thingSoC/TSOC_Teensy3x/TSOC_Teensy3x/eagleUp/eagleUp_TSOC_Teensy3X_board_bottom.jpg

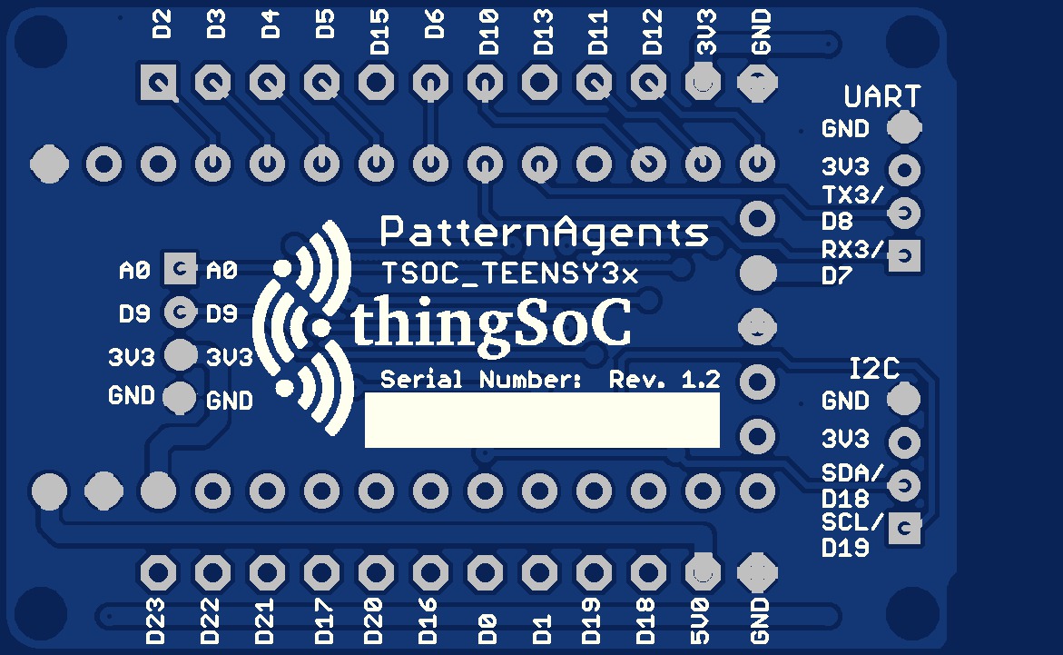
TSOC_Teensy3x/eagleUp/eagleUp_TSOC_Teensy3X_board_bottom.jpg
