thingSoC/TSOC_Teensy3x/TSOC_Teensy3x/eagleUp/eagleUp_TSOC_Teensy3X_board_top.jpg

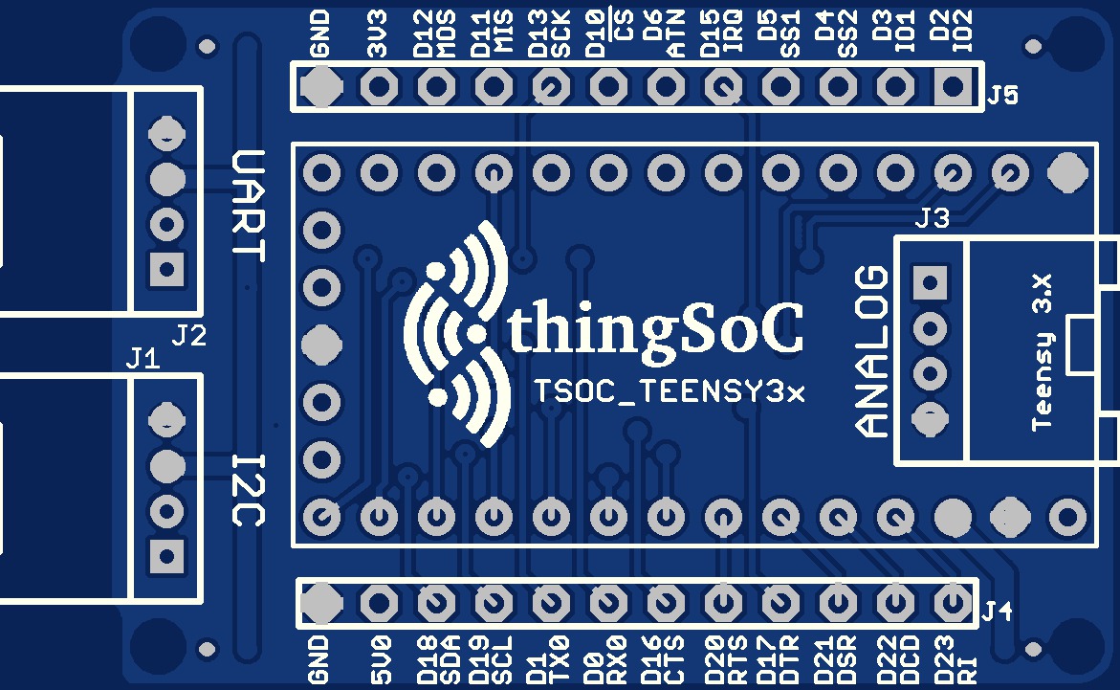
TSOC_Teensy3x/eagleUp/eagleUp_TSOC_Teensy3X_board_top.jpg
