thingSoC/TSOC_Teensy3x/TSOC_Teensy3x/images/product/TSOC_Teensy3x_click.jpg

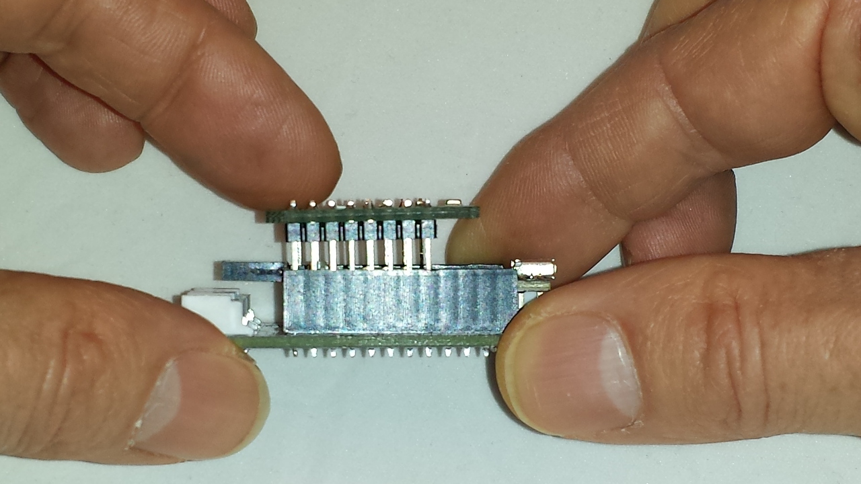
TSOC_Teensy3x/images/product/TSOC_Teensy3x_click.jpg
