thingSoC/TSOC_Teensy3x/TSOC_Teensy3x/images/product/TSOC_Teensy3x_pcb.png

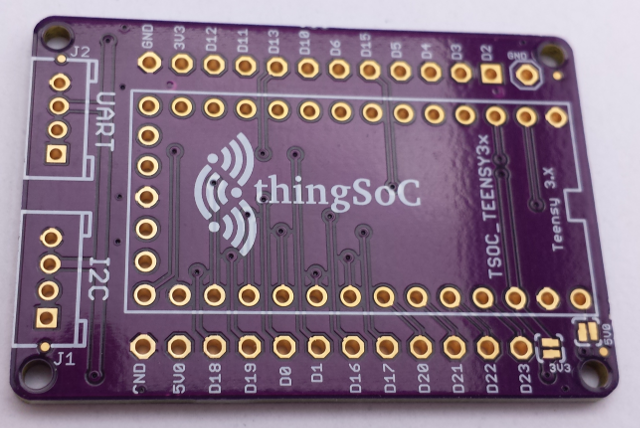
TSOC_Teensy3x/images/product/TSOC_Teensy3x_pcb.png
