thingSoC/TSOC_Teensy3x/TSOC_Teensy3x/images/product/TSOC_Teensy3x_pop_top.png

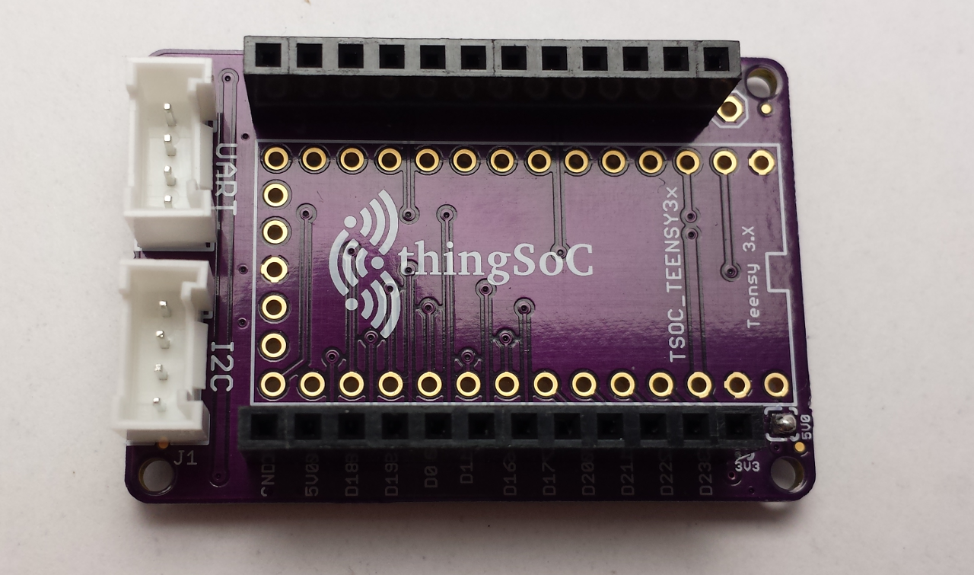
TSOC_Teensy3x/images/product/TSOC_Teensy3x_pop_top.png
