thingSoC/TSOC_Teensy3x/TSOC_Teensy3x/images/product/TSOC_Teensy3x_R1_0.png

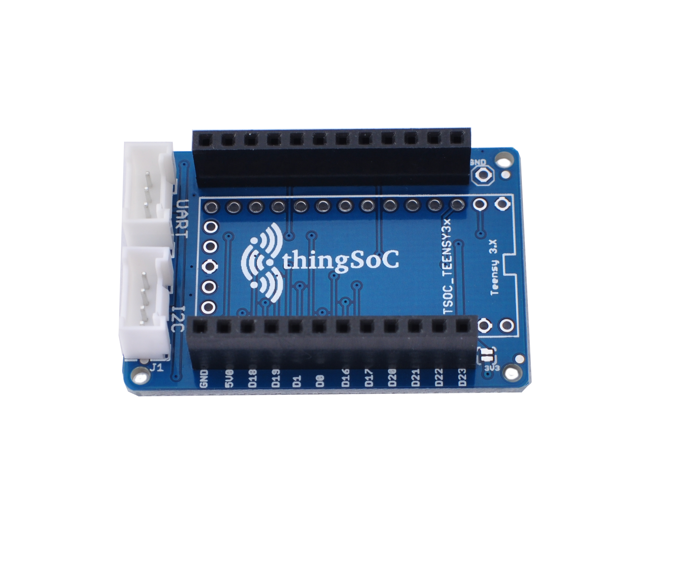
TSOC_Teensy3x/images/product/TSOC_Teensy3x_R1_0.png
