thingSoC/TSOC_Teensy3x/TSOC_Teensy3x/images/product/TSOC_Teensy3x_USB1.jpg

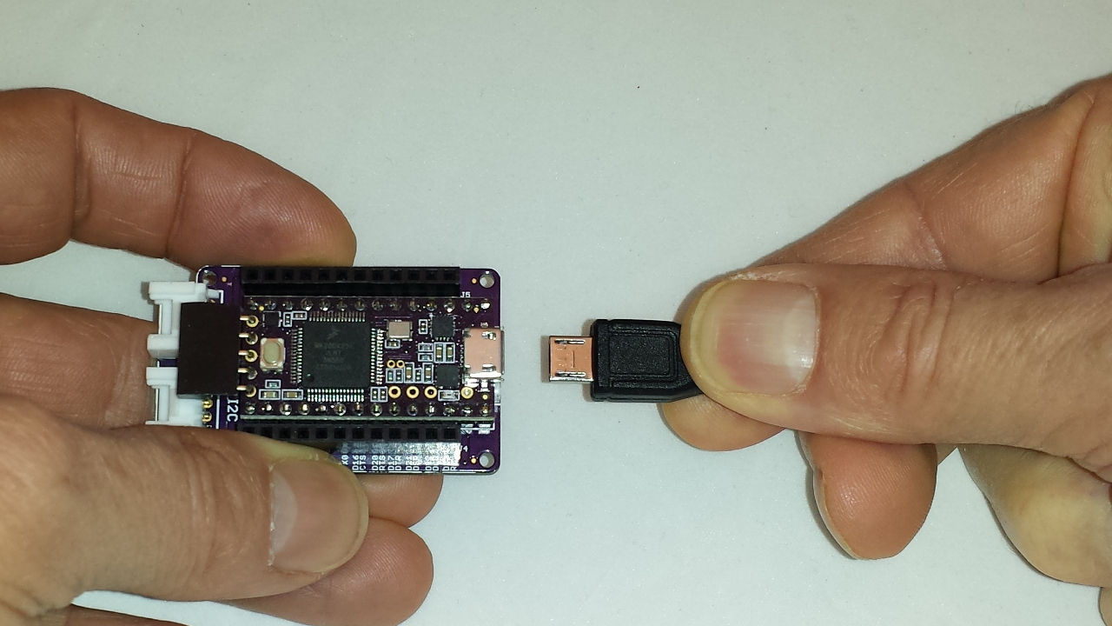
TSOC_Teensy3x/images/product/TSOC_Teensy3x_USB1.jpg
