thingSoC/TSOC_Teensy3x/TSOC_Teensy3x/images/product/TSOC_Teensy3x_with_Click3.png

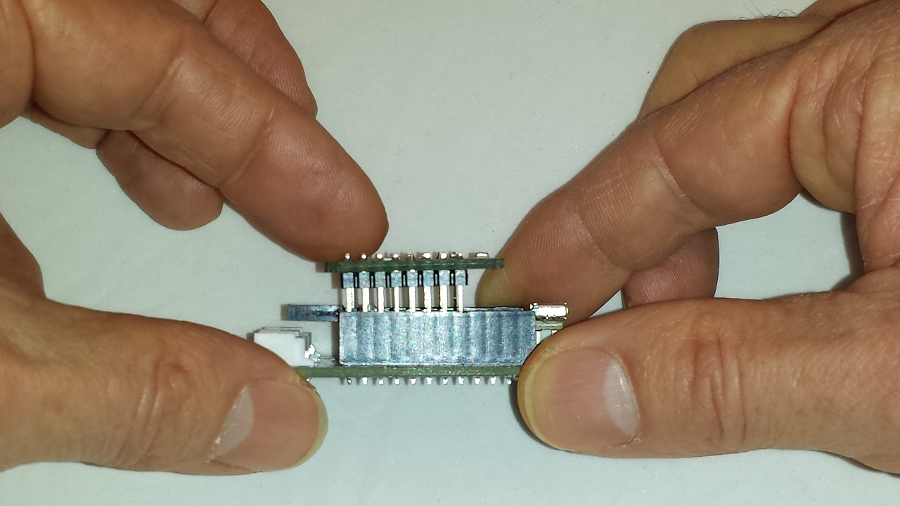
TSOC_Teensy3x/images/product/TSOC_Teensy3x_with_Click3.png
