thingSoC/TSOC_Teensy3x/TSOC_Teensy3x/images/TSOC_Teensy3x_iso.png

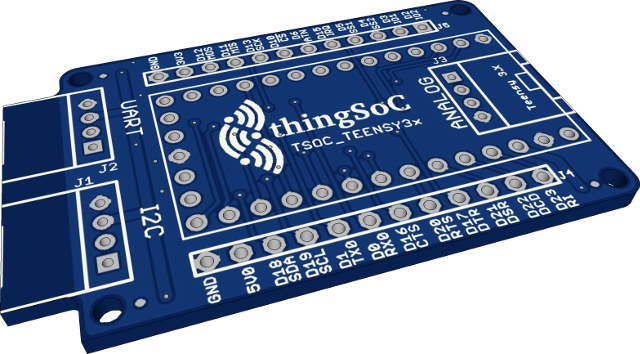
TSOC_Teensy3x/images/TSOC_Teensy3x_iso.png
