thingSoC/TSOC_Teensy3x/TSOC_Teensy3x/revisions/R1_0/TSOC_Teensy3X_brd.pdf

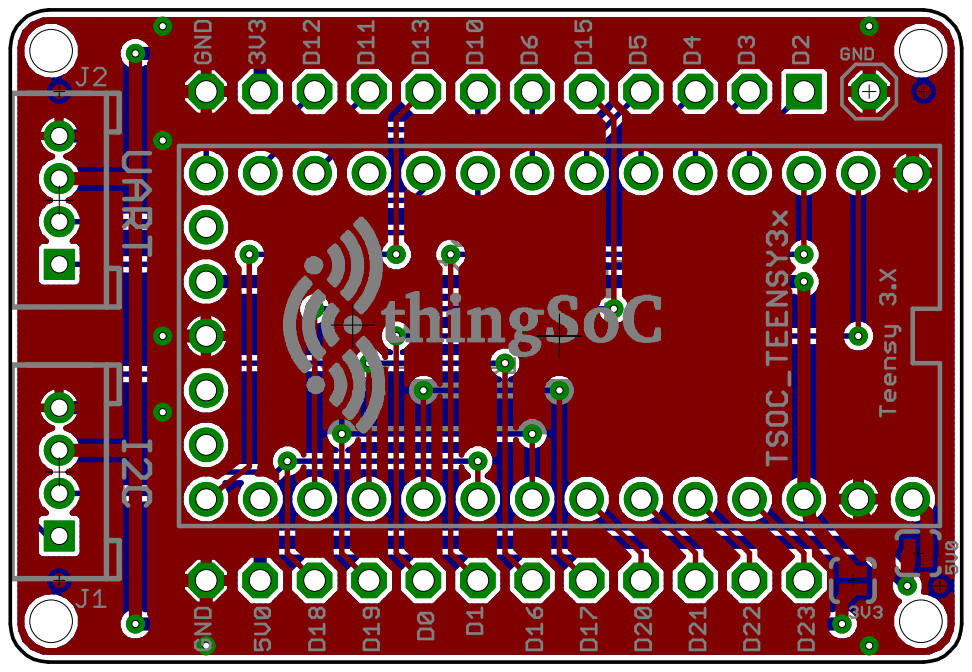
[picture p49: page 1]
