thingSoC/TSOC_Teensy3x/TSOC_Teensy3x/revisions/R1_0/TSOC_Teensy3X_bsilk.pdf

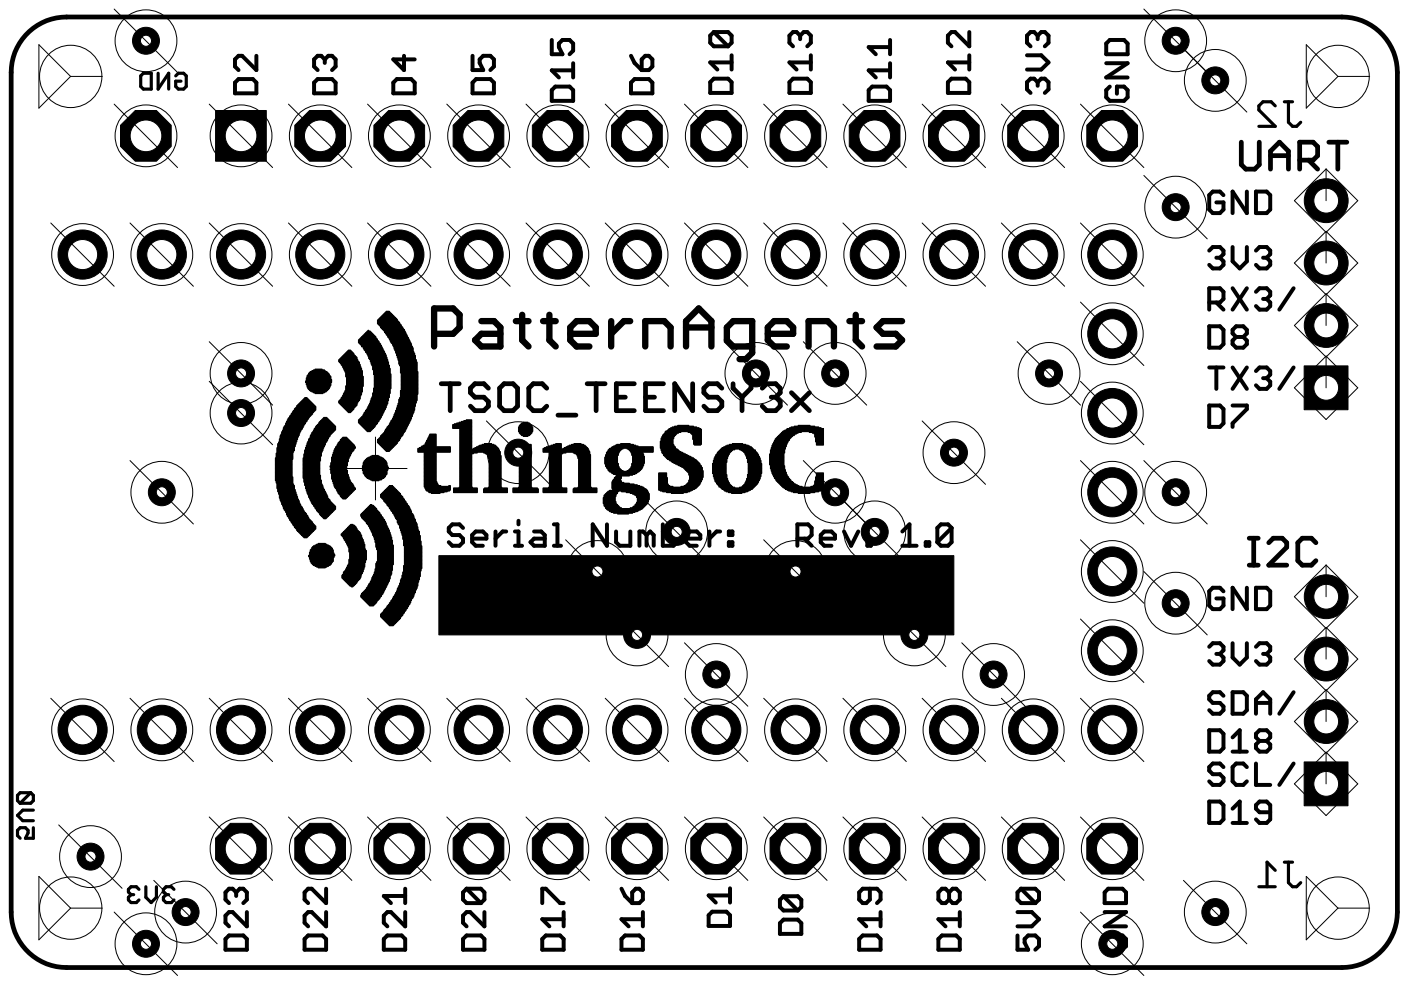
[picture p50: page 1]
