thingSoC/TSOC_Teensy3x/TSOC_Teensy3x/revisions/R1_0/TSOC_Teensy3X_sch.pdf

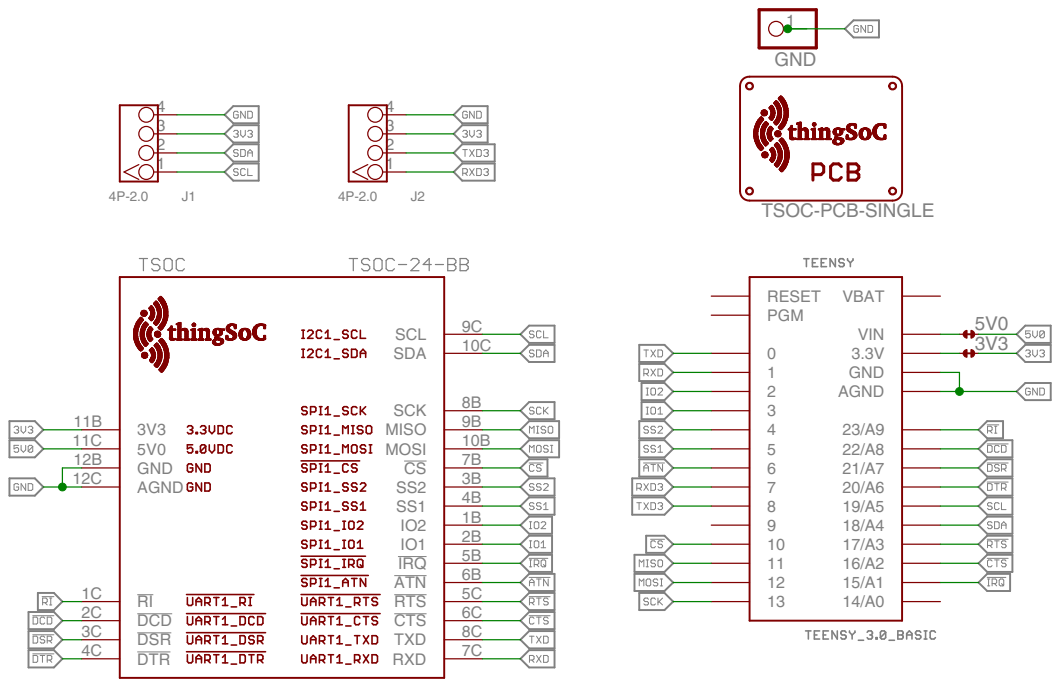
[picture p51: page 1]
