thingSoC/TSOC_Teensy3x/TSOC_Teensy3x/revisions/R1_0/TSOC_Teensy3X_sch_black.pdf

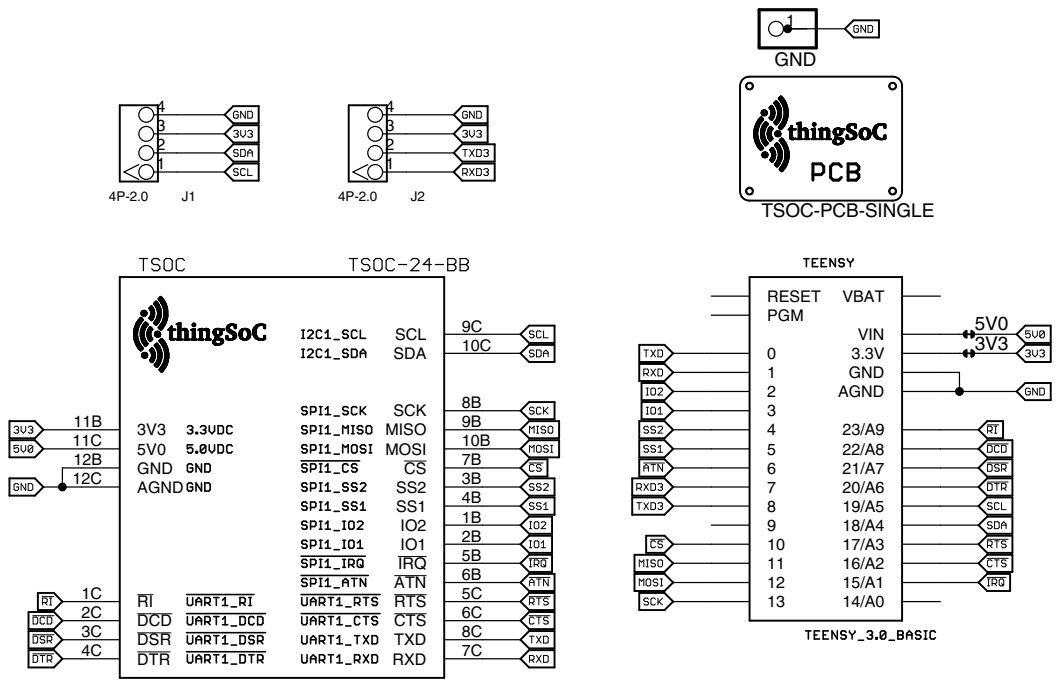
[picture p52: page 1]
