thingSoC/TSOC_Teensy3x/TSOC_Teensy3x/revisions/R1_0/TSOC_Teensy3X_tsilk.pdf

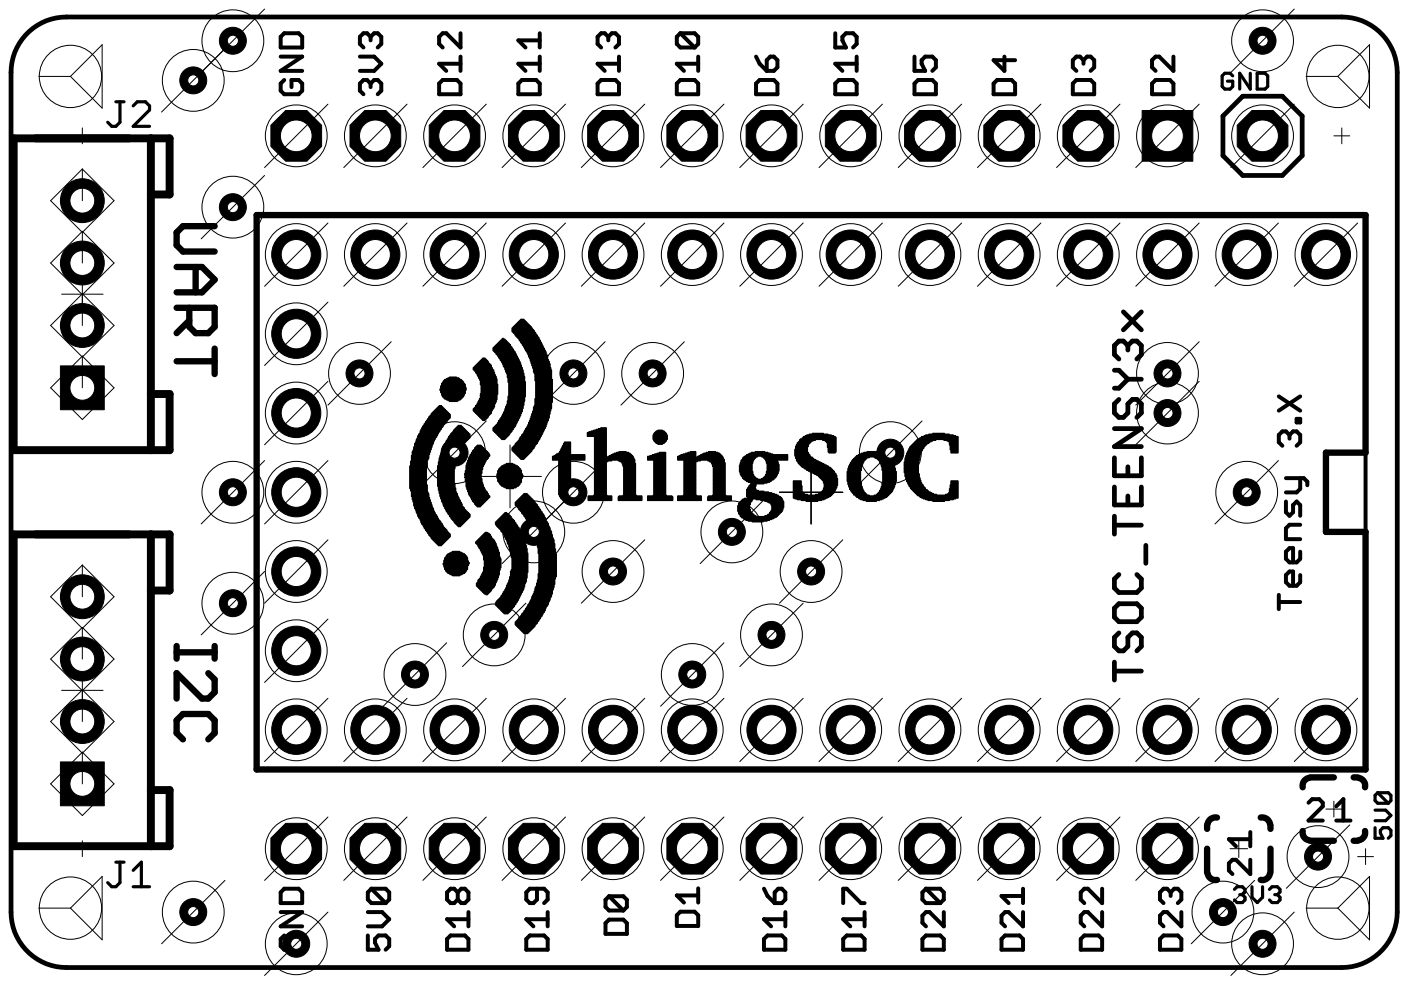
[picture p53: page 1]
